ajacocks/mb386sx-rc2016/KiCad/AT386SX.kicad_sch

## KiCad design KiCad/AT386SX.kicad_sch (2026-02-18)

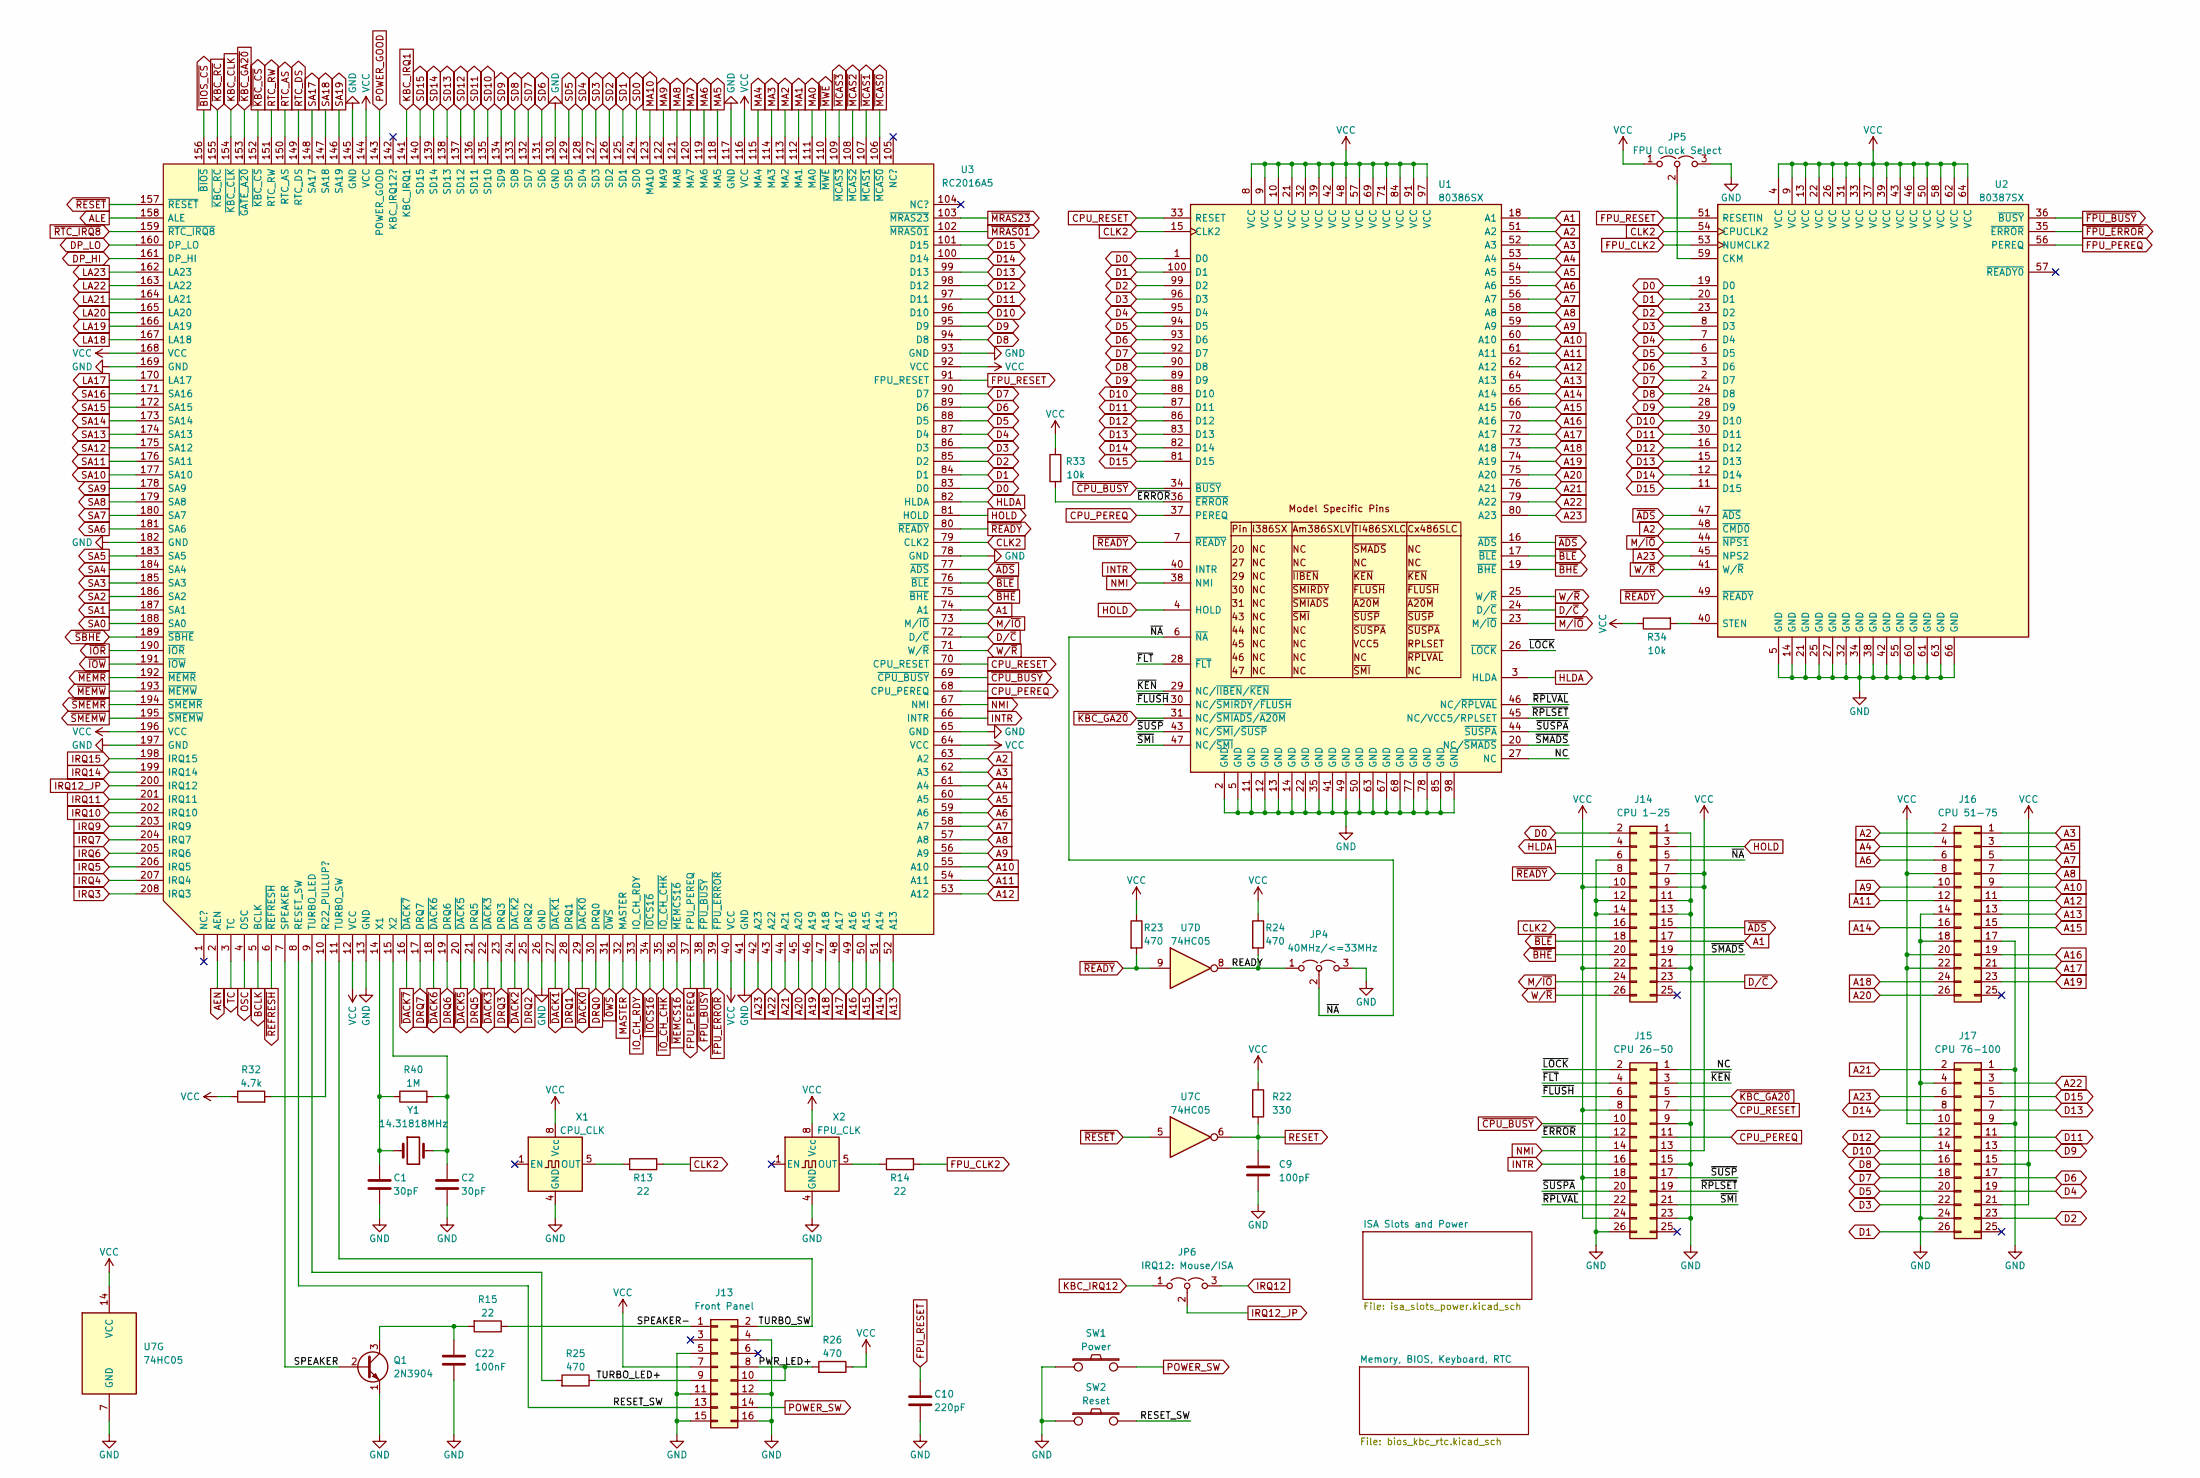
[picture p5: schematic AT386SX.kicad_sch]

Parts:
C1, C2: 30pF; Cap_Cer_508
C9: 100pF; Cap_Cer_508
C10: 220pF; Cap_Cer_508
C22: 100nF; Cap_Cer_508
J13: Front Panel; Conn_Pin_Header_8x2_2.54mm
J14: CPU 1-25; PinHeader_2x13_P2.00mm_Vertical
J15: CPU 26-50; PinHeader_2x13_P2.00mm_Vertical
J16: CPU 51-75; PinHeader_2x13_P2.00mm_Vertical
J17: CPU 76-100; PinHeader_2x13_P2.00mm_Vertical
JP4: 40MHz/<=33MHz; Conn_Pin_Header_3x1_2.54mm
JP5: FPU Clock Select; Conn_Pin_Header_3x1_2.54mm
JP6: IRQ12: Mouse/ISA; Conn_Pin_Header_3x1_2.54mm
Q1: 2N3904; Transistor_TO92_EBC_254
R13, R14, R15: 22; Res_762
R22: 330; Res_762
R23, R24, R25, R26: 470; Res_762
R32: 4.7k; Res_762
R33, R34: 10k; Res_762
R40: 1M; Res_762
SW1: Power; Switch_Tactile_6mm
SW2: Reset; Switch_Tactile_6mm
U1: 80386SX; PQFP-100_19x19mm_P0.635mm_i386sx
U2: 80387SX; IC_PLCC68_INTEL_TH
U3: RC2016A5; PQFP-208_28x28mm_P0.5mm
U7: 74HC05; IC_DIP14_300
X1: CPU_CLK; OSC_Half_Can_DIP8
X2: FPU_CLK; OSC_Half_Can_DIP8
Y1: 14.31818MHz; Crystal_HC-49U_Vert

Connections:
A1: J14.17, U1.18 (A1), U3.74 (A1)
A2: J16.2, U1.51 (A2), U2.48 (~CMD0), U3.63 (A2)
A3: J16.1, U1.52 (A3), U3.62 (A3)
A4: J16.4, U1.53 (A4), U3.61 (A4)
A5: J16.3, U1.54 (A5), U3.60 (A5)
A6: J16.6, U1.55 (A6), U3.59 (A6)
A7: J16.5, U1.56 (A7), U3.58 (A7)
A8: J16.7, U1.58 (A8), U3.57 (A8)
A9: J16.10, U1.59 (A9), U3.56 (A9)
A10: J16.9, U1.60 (A10), U3.55 (A10)
A11: J16.12, U1.61 (A11), U3.54 (A11)
A12: J16.11, U1.62 (A12), U3.53 (A12)
A13: J16.13, U1.64 (A13), U3.52 (A13)
A14: J16.16, U1.65 (A14), U3.51 (A14)
A15: J16.15, U1.66 (A15), U3.50 (A15)
A16: J16.19, U1.70 (A16), U3.49 (A16)
A17: J16.21, U1.72 (A17), U3.48 (A17)
A18: J16.24, U1.73 (A18), U3.47 (A18)
A19: J16.23, U1.74 (A19), U3.46 (A19)
A20: J16.26, U1.75 (A20), U3.45 (A20)
A21: J17.2, U1.76 (A21), U3.44 (A21)
A22: J17.3, U1.79 (A22), U3.43 (A22)
A23: J17.6, U1.80 (A23), U2.45 (NPS2), U3.42 (A23)
AEN: U3.2 (AEN)
ALE: U3.158 (ALE)
BCLK: U3.5 (BCLK)
CLK2: J14.16, R13.2, U1.15 (CLK2), U2.54 (CPUCLK2), U3.79 (CLK2)
CPU_PEREQ: J15.11, U1.37 (PEREQ), U3.68 (CPU_PEREQ)
CPU_RESET: J15.7, U1.33 (RESET), U3.70 (CPU_RESET)
D0: J14.2, U1.1 (D0), U2.19 (D0), U3.83 (D0)
D1: J17.26, U1.100 (D1), U2.20 (D1), U3.84 (D1)
D2: J17.23, U1.99 (D2), U2.23 (D2), U3.85 (D2)
D3: J17.22, U1.96 (D3), U2.8 (D3), U3.86 (D3)
D4: J17.19, U1.95 (D4), U2.7 (D4), U3.87 (D4)
D5: J17.20, U1.94 (D5), U2.6 (D5), U3.88 (D5)
D6: J17.17, U1.93 (D6), U2.3 (D6), U3.89 (D6)
D7: J17.18, U1.92 (D7), U2.2 (D7), U3.90 (D7)
D8: J17.16, U1.90 (D8), U2.24 (D8), U3.94 (D8)
D9: J17.13, U1.89 (D9), U2.28 (D9), U3.95 (D9)
D10: J17.14, U1.88 (D10), U2.29 (D10), U3.96 (D10)
D11: J17.11, U1.87 (D11), U2.30 (D11), U3.97 (D11)
D12: J17.12, U1.86 (D12), U2.16 (D12), U3.98 (D12)
D13: J17.7, U1.83 (D13), U2.15 (D13), U3.99 (D13)
D14: J17.8, U1.82 (D14), U2.12 (D14), U3.100 (D14)
D15: J17.5, U1.81 (D15), U2.11 (D15), U3.101 (D15)
DP_HI: U3.161 (DP_HI)
DP_LO: U3.160 (DP_LO)
DRQ0: U3.30 (DRQ0)
DRQ1: U3.28 (DRQ1)
DRQ2: U3.25 (DRQ2)
DRQ3: U3.23 (DRQ3)
DRQ5: U3.21 (DRQ5)
DRQ6: U3.19 (DRQ6)
DRQ7: U3.17 (DRQ7)
D/~C: J14.23, U1.24 (D/~C), U3.72 (D/~C)
FPU_CLK2: R14.2, U2.53 (NUMCLK2)
FPU_PEREQ: U2.56 (PEREQ), U3.37 (FPU_PEREQ)
FPU_RESET: C10.1, U2.51 (RESETIN), U3.91 (FPU_RESET)
GND: C1.2, C2.2, C9.2, C10.2, C22.2, J13.4, J13.5, J13.11, J13.12, J13.15, J13.16, J14.1, J14.6, J14.11, J14.12, J14.13, J14.14, J14.21, J15.9, J15.15, J15.23, J15.26, J16.14, J16.17, J16.18, J17.1, J17.4, J17.9, J17.24, JP4.3 (B), JP5.3 (B), Q1.1 (E), SW1.1, SW2.1, U1.2 (GND), U1.5 (GND), U1.11 (GND), U1.12 (GND), U1.13 (GND), U1.14 (GND), U1.22 (GND), U1.35 (GND), U1.41 (GND), U1.49 (GND), U1.50 (GND), U1.63 (GND), U1.67 (GND), U1.68 (GND), U1.77 (GND), U1.78 (GND), U1.85 (GND), U1.98 (GND), U2.5 (GND), U2.14 (GND), U2.21 (GND), U2.25 (GND), U2.27 (GND), U2.32 (GND), U2.34 (GND), U2.38 (GND), U2.42 (GND), U2.55 (GND), U2.60 (GND), U2.61 (GND), U2.63 (GND), U2.66 (GND), U3.13 (GND), U3.26 (GND), U3.41 (GND), U3.65 (GND), U3.78 (GND), U3.93 (GND), U3.117 (GND), U3.130 (GND), U3.145 (GND), U3.169 (GND), U3.182 (GND), U3.197 (GND), U7.7 (GND), X1.4 (GND), X2.4 (GND)
HLDA: J14.4, U1.3 (HLDA), U3.82 (HLDA)
HOLD: J14.3, U1.4 (HOLD), U3.81 (HOLD)
INTR: J15.16, U1.40 (INTR), U3.66 (INTR)
IO_CH_RDY: U3.33 (IO_CH_RDY)
IRQ3: U3.208 (IRQ3)
IRQ4: U3.207 (IRQ4)
IRQ5: U3.206 (IRQ5)
IRQ6: U3.205 (IRQ6)
IRQ7: U3.204 (IRQ7)
IRQ9: U3.203 (IRQ9)
IRQ10: U3.202 (IRQ10)
IRQ11: U3.201 (IRQ11)
IRQ12: JP6.3 (B)
IRQ12_JP: JP6.2 (C), U3.200 (IRQ12)
IRQ14: U3.199 (IRQ14)
IRQ15: U3.198 (IRQ15)
KBC_CLK: U3.154 (~KBC_CLK)
KBC_IRQ1: U3.141 (KBC_IRQ1)
KBC_IRQ12: JP6.1 (A)
LA17: U3.170 (LA17)
LA18: U3.167 (LA18)
LA19: U3.166 (LA19)
LA20: U3.165 (LA20)
LA21: U3.164 (LA21)
LA22: U3.163 (LA22)
LA23: U3.162 (LA23)
MA0: U3.111 (MA0)
MA1: U3.112 (MA1)
MA2: U3.113 (MA2)
MA3: U3.114 (MA3)
MA4: U3.115 (MA4)
MA5: U3.118 (MA5)
MA6: U3.119 (MA6)
MA7: U3.120 (MA7)
MA8: U3.121 (MA8)
MA9: U3.122 (MA9)
MA10: U3.123 (MA10)
MASTER: U3.32 (MASTER)
M/~IO: J14.24, U1.23 (M/~IO), U2.44 (~NPS1), U3.73 (M/~IO)
NC: J15.1, U1.27 (NC)
NMI: J15.14, U1.38 (NMI), U3.67 (NMI)
unnamed: C1.1, R40.1, U3.14 (X1), Y1.1
unnamed: C2.1, R40.2, U3.15 (X2), Y1.2
unnamed: C22.1, Q1.3 (C), R15.2
unnamed: JP5.2 (C), U2.59 (CKM)
unnamed: R13.1, X1.5 (OUT)
unnamed: R14.1, X2.5 (OUT)
unnamed: R25.2, U3.9 (TURBO_LED)
unnamed: R32.2, U3.10 (R22_PULLUP?)
unnamed: R34.2, U2.40 (STEN)
OSC: U3.4 (OSC)
POWER_GOOD: U3.143 (POWER_GOOD)
POWER_SW: J13.14, SW1.2
PWR_LED+: J13.8, J13.10, R26.2
READY: JP4.1 (A), R24.2, U7.8
RESET: C9.1, R22.2, U7.6
RESET_SW: J13.13, SW2.2, U3.8 (RESET_SW)
RTC_AS: U3.150 (RTC_AS)
RTC_DS: U3.149 (RTC_DS)
RTC_RW: U3.151 (RTC_RW)
SA0: U3.188 (SA0)
SA1: U3.187 (SA1)
SA2: U3.186 (SA2)
SA3: U3.185 (SA3)
SA4: U3.184 (SA4)
SA5: U3.183 (SA5)
SA6: U3.181 (SA6)
SA7: U3.180 (SA7)
SA8: U3.179 (SA8)
SA9: U3.178 (SA9)
SA10: U3.177 (SA10)
SA11: U3.176 (SA11)
SA12: U3.175 (SA12)
SA13: U3.174 (SA13)
SA14: U3.173 (SA14)
SA15: U3.172 (SA15)
SA16: U3.171 (SA16)
SA17: U3.148 (SA17)
SA18: U3.147 (SA18)
SA19: U3.146 (SA19)
SD0: U3.124 (SD0)
SD1: U3.125 (SD1)
SD2: U3.126 (SD2)
SD3: U3.127 (SD3)
SD4: U3.128 (SD4)
SD5: U3.129 (SD5)
SD6: U3.131 (SD6)
SD7: U3.132 (SD7)
SD8: U3.133 (SD8)
SD9: U3.134 (SD9)
SD10: U3.135 (SD10)
SD11: U3.136 (SD11)
SD12: U3.137 (SD12)
SD13: U3.138 (SD13)
SD14: U3.139 (SD14)
SD15: U3.140 (SD15)
SPEAKER: Q1.2 (B), U3.7 (SPEAKER)
SPEAKER-: J13.1, R15.1
TC: U3.3 (TC)
TURBO_LED+: J13.9, R25.1
TURBO_SW: J13.2, U3.11 (TURBO_SW)
VCC: J13.7, J14.7, J14.9, J14.10, J14.22, J15.8, J15.13, J15.18, J15.24, J16.8, J16.20, J16.22, J17.10, J17.15, J17.21, JP5.1 (A), R22.1, R23.1, R24.1, R26.1, R32.1, R33.1, R34.1, U1.8 (VCC), U1.9 (VCC), U1.10 (VCC), U1.21 (VCC), U1.32 (VCC), U1.39 (VCC), U1.42 (VCC), U1.48 (VCC), U1.57 (VCC), U1.69 (VCC), U1.71 (VCC), U1.84 (VCC), U1.91 (VCC), U1.97 (VCC), U2.4 (VCC), U2.9 (VCC), U2.13 (VCC), U2.22 (VCC), U2.26 (VCC), U2.31 (VCC), U2.33 (VCC), U2.37 (VCC), U2.39 (VCC), U2.43 (VCC), U2.46 (VCC), U2.50 (VCC), U2.58 (VCC), U2.62 (VCC), U2.64 (VCC), U3.12 (VCC), U3.40 (VCC), U3.64 (VCC), U3.92 (VCC), U3.116 (VCC), U3.144 (VCC), U3.168 (VCC), U3.196 (VCC), U7.14 (VCC), X1.8 (Vcc), X2.8 (Vcc)
W/~R: J14.26, U1.25 (W/~R), U2.41 (W/~R), U3.71 (W/~R)
~0WS: U3.31 (~0WS)
~ADS: J14.15, U1.16 (~ADS), U2.47 (~ADS), U3.77 (~ADS)
~BHE: J14.20, U1.19 (~BHE), U3.75 (~BHE)
~BIOS_CS: U3.156 (~BIOS)
~BLE: J14.18, U1.17 (~BLE), U3.76 (~BLE)
~CPU_BUSY: J15.10, U1.34 (~BUSY), U3.69 (~CPU_BUSY)
~DACK0: U3.29 (~DACK0)
~DACK1: U3.27 (~DACK1)
~DACK2: U3.24 (~DACK2)
~DACK3: U3.22 (~DACK3)
~DACK5: U3.20 (~DACK5)
~DACK6: U3.18 (~DACK6)
~DACK7: U3.16 (~DACK7)
~ERROR: J15.12, R33.2, U1.36 (~ERROR)
~FLT: J15.4, U1.28 (~FLT)
~FLUSH: J15.6, U1.30 (NC/~SMIRDY/~FLUSH)
~FPU_BUSY: U2.36 (~BUSY), U3.38 (~FPU_BUSY)
~FPU_ERROR: U2.35 (~ERROR), U3.39 (~FPU_ERROR)
~IOCS16: U3.34 (~IOCS16)
~IOR: U3.190 (~IOR)
~IOW: U3.191 (~IOW)
~IO_CH_CHK: U3.35 (~IO_CH_CHK)
~KBC_CS: U3.152 (~KBC_CS)
~KBC_GA20: J15.5, U1.31 (NC/~SMIADS/~A20M), U3.153 (~GATE_A20)
~KBC_RC: U3.155 (~KBC_RC)
~KEN: J15.3, U1.29 (NC/~IIBEN/~KEN)
~LOCK: J15.2, U1.26 (~LOCK)
~MCAS0: U3.106 (~MCAS0)
~MCAS1: U3.107 (~MCAS1)
~MCAS2: U3.108 (~MCAS2)
~MCAS3: U3.109 (~MCAS3)
~MEMCS16: U3.36 (~MEMCS16)
~MEMR: U3.192 (~MEMR)
~MEMW: U3.193 (~MEMW)
~MRAS01: U3.102 (~MRAS01)
~MRAS23: U3.103 (~MRAS23)
~MWE: U3.110 (~MWE)
~NA: J14.5, JP4.2 (C), U1.6 (~NA)
~READY: J14.8, R23.2, U1.7 (~READY), U2.49 (~READY), U3.80 (~READY), U7.9
~REFRESH: U3.6 (~REFRESH)
~RESET: U3.157 (~RESET), U7.5
~RPLSET: J15.19, U1.45 (NC/VCC5/RPLSET)
~RPLVAL: J15.22, U1.46 (NC/~RPLVAL)
~RTC_IRQ8: U3.159 (~RTC_IRQ8)
~SBHE: U3.189 (~SBHE)
~SMADS: J14.19, U1.20 (NC/~SMADS)
~SMEMR: U3.194 (~SMEMR)
~SMEMW: U3.195 (~SMEMW)
~SMI: J15.21, U1.47 (NC/~SMI)
~SUSPA: J15.20, U1.44 (~SUSPA)
~SUSP: J15.17, U1.43 (NC/~SMI/~SUSP)
