ajacocks/mb386sx-rc2016/KiCad/bios_kbc_rtc.kicad_sch

## KiCad design KiCad/bios_kbc_rtc.kicad_sch (2026-02-17)

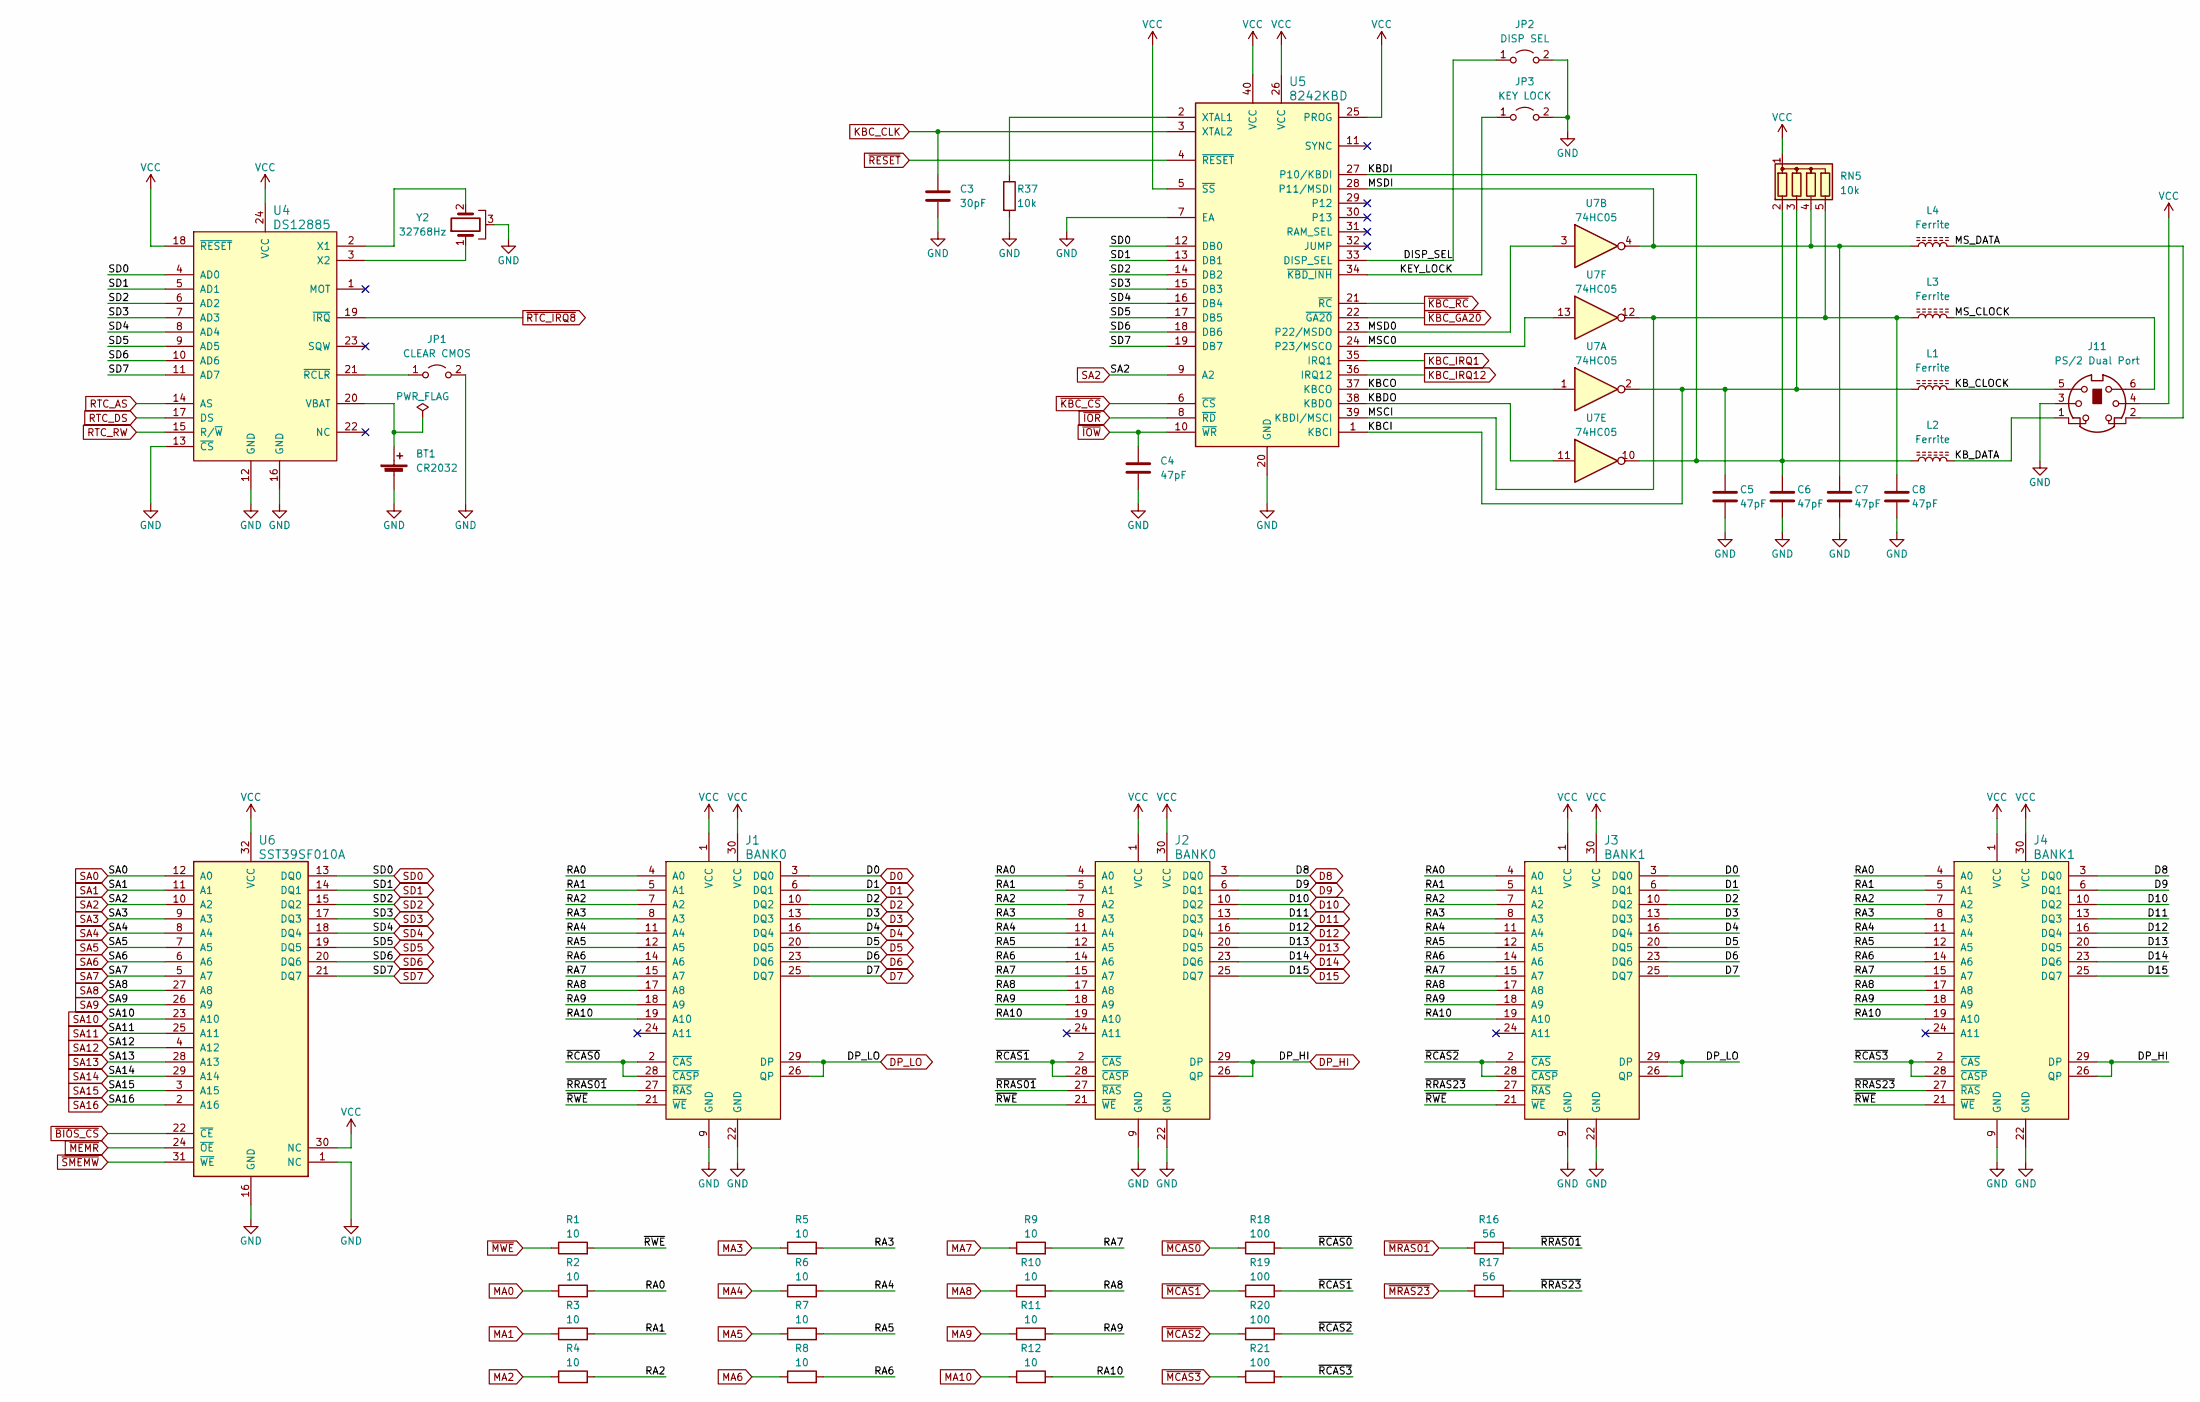
[picture p6: schematic bios_kbc_rtc.kicad_sch]

Parts:
BT1: CR2032; Battery_Holder_CR2032_Universal
C3: 30pF; Cap_Cer_508
C4, C5, C6, C7, C8: 47pF; Cap_Cer_508
J1, J2: BANK0; Conn_SIMM30
J3, J4: BANK1; Conn_SIMM30
J11: PS/2 Dual Port; Conn_Mini_DIN_6pin
JP1: CLEAR CMOS; Conn_Pin_Header_2x1_2.54mm
JP2: DISP SEL; Conn_Pin_Header_2x1_2.54mm
JP3: KEY LOCK; Conn_Pin_Header_2x1_2.54mm
L1, L2, L3, L4: Ferrite; L_Ferrite_1016
R1, R2, R3, R4, R5, R6, R7, R8, R9, R10, R11, R12: 10; Res_762
R16, R17: 56; Res_762
R18, R19, R20, R21: 100; Res_762
R37: 10k; Res_762
RN5: 10k; Conn_SIL5
U4: DS12885; IC_DIP24_600
U5: 8242KBD; IC_DIP40_600
U6: SST39SF010A; IC_DIP32_600
U7: 74HC05; IC_DIP14_300
Y2: 32768Hz; Crystal_32K_Horiz

Connections:
D0: J1.3 (DQ0), J3.3 (DQ0)
D1: J1.6 (DQ1), J3.6 (DQ1)
D2: J1.10 (DQ2), J3.10 (DQ2)
D3: J1.13 (DQ3), J3.13 (DQ3)
D4: J1.16 (DQ4), J3.16 (DQ4)
D5: J1.20 (DQ5), J3.20 (DQ5)
D6: J1.23 (DQ6), J3.23 (DQ6)
D7: J1.25 (DQ7), J3.25 (DQ7)
D8: J2.3 (DQ0), J4.3 (DQ0)
D9: J2.6 (DQ1), J4.6 (DQ1)
D10: J2.10 (DQ2), J4.10 (DQ2)
D11: J2.13 (DQ3), J4.13 (DQ3)
D12: J2.16 (DQ4), J4.16 (DQ4)
D13: J2.20 (DQ5), J4.20 (DQ5)
D14: J2.23 (DQ6), J4.23 (DQ6)
D15: J2.25 (DQ7), J4.25 (DQ7)
DISP_SEL: JP2.1 (A), U5.33 (DISP_SEL)
DP_HI: J2.26 (QP), J2.29 (DP), J4.26 (QP), J4.29 (DP)
DP_LO: J1.26 (QP), J1.29 (DP), J3.26 (QP), J3.29 (DP)
GND: BT1.2 (-), C3.2, C4.2, C5.2, C6.2, C7.2, C8.2, J1.9 (GND), J1.22 (GND), J2.9 (GND), J2.22 (GND), J3.9 (GND), J3.22 (GND), J4.9 (GND), J4.22 (GND), J11.3, JP1.2 (B), JP2.2 (B), JP3.2 (B), R37.2, U4.12 (GND), U4.13 (~CS), U4.16 (GND), U5.7 (EA), U5.20 (GND), U6.1 (NC), U6.16 (GND), Y2.3
KBCI: C5.1, L1.1, RN5.3 (R2), U5.1 (KBCI), U7.2
KBCO: U5.37 (KBCO), U7.1
KBC_CLK: C3.1, U5.3 (XTAL2)
KBC_IRQ1: U5.35 (IRQ1)
KBC_IRQ12: U5.36 (IRQ12)
KBDI: C6.1, L2.1, RN5.2 (R1), U5.27 (P10/KBDI), U7.10
KBDO: U5.38 (KBDO), U7.11
KB_CLOCK: J11.5, L1.2
KB_DATA: J11.1, L2.2
KEY_LOCK: JP3.1 (A), U5.34 (~KBD_INH)
MA0: R2.1
MA1: R3.1
MA2: R4.1
MA3: R5.1
MA4: R6.1
MA5: R7.1
MA6: R8.1
MA7: R9.1
MA8: R10.1
MA9: R11.1
MA10: R12.1
MSC0: U5.24 (P23/MSCO), U7.13
MSCI: C8.1, L3.1, RN5.5 (R4), U5.39 (KBDI/MSCI), U7.12
MSD0: U5.23 (P22/MSDO), U7.3
MSDI: C7.1, L4.1, RN5.4 (R3), U5.28 (P11/MSDI), U7.4
MS_CLOCK: J11.6, L3.2
MS_DATA: J11.2, L4.2
unnamed: BT1.1 (+), U4.20 (VBAT)
unnamed: JP1.1 (A), U4.21 (~RCLR)
unnamed: R37.1, U5.2 (XTAL1)
unnamed: U4.2 (X1), Y2.2
unnamed: U4.3 (X2), Y2.1
RA0: J1.4 (A0), J2.4 (A0), J3.4 (A0), J4.4 (A0), R2.2
RA1: J1.5 (A1), J2.5 (A1), J3.5 (A1), J4.5 (A1), R3.2
RA2: J1.7 (A2), J2.7 (A2), J3.7 (A2), J4.7 (A2), R4.2
RA3: J1.8 (A3), J2.8 (A3), J3.8 (A3), J4.8 (A3), R5.2
RA4: J1.11 (A4), J2.11 (A4), J3.11 (A4), J4.11 (A4), R6.2
RA5: J1.12 (A5), J2.12 (A5), J3.12 (A5), J4.12 (A5), R7.2
RA6: J1.14 (A6), J2.14 (A6), J3.14 (A6), J4.14 (A6), R8.2
RA7: J1.15 (A7), J2.15 (A7), J3.15 (A7), J4.15 (A7), R9.2
RA8: J1.17 (A8), J2.17 (A8), J3.17 (A8), J4.17 (A8), R10.2
RA9: J1.18 (A9), J2.18 (A9), J3.18 (A9), J4.18 (A9), R11.2
RA10: J1.19 (A10), J2.19 (A10), J3.19 (A10), J4.19 (A10), R12.2
RTC_AS: U4.14 (AS)
RTC_DS: U4.17 (DS)
RTC_RW: U4.15 (R/~W)
SA0: U6.12 (A0)
SA1: U6.11 (A1)
SA2: U5.9 (A2), U6.10 (A2)
SA3: U6.9 (A3)
SA4: U6.8 (A4)
SA5: U6.7 (A5)
SA6: U6.6 (A6)
SA7: U6.5 (A7)
SA8: U6.27 (A8)
SA9: U6.26 (A9)
SA10: U6.23 (A10)
SA11: U6.25 (A11)
SA12: U6.4 (A12)
SA13: U6.28 (A13)
SA14: U6.29 (A14)
SA15: U6.3 (A15)
SA16: U6.2 (A16)
SD0: U4.4 (AD0), U5.12 (DB0), U6.13 (DQ0)
SD1: U4.5 (AD1), U5.13 (DB1), U6.14 (DQ1)
SD2: U4.6 (AD2), U5.14 (DB2), U6.15 (DQ2)
SD3: U4.7 (AD3), U5.15 (DB3), U6.17 (DQ3)
SD4: U4.8 (AD4), U5.16 (DB4), U6.18 (DQ4)
SD5: U4.9 (AD5), U5.17 (DB5), U6.19 (DQ5)
SD6: U4.10 (AD6), U5.18 (DB6), U6.20 (DQ6)
SD7: U4.11 (AD7), U5.19 (DB7), U6.21 (DQ7)
VCC: J1.1 (VCC), J1.30 (VCC), J2.1 (VCC), J2.30 (VCC), J3.1 (VCC), J3.30 (VCC), J4.1 (VCC), J4.30 (VCC), J11.4, RN5.1 (common), U4.18 (~RESET), U4.24 (VCC), U5.5 (~SS), U5.25 (PROG), U5.26 (VCC), U5.40 (VCC), U6.30 (NC), U6.32 (VCC)
~BIOS_CS: U6.22 (~CE)
~IOR: U5.8 (~RD)
~IOW: C4.1, U5.10 (~WR)
~KBC_CS: U5.6 (~CS)
~KBC_GA20: U5.22 (~GA20)
~KBC_RC: U5.21 (~RC)
~MCAS0: R18.1
~MCAS1: R19.1
~MCAS2: R20.1
~MCAS3: R21.1
~MEMR: U6.24 (~OE)
~MRAS01: R16.1
~MRAS23: R17.1
~MWE: R1.1
~RCAS0: J1.2 (~CAS), J1.28 (~CASP), R18.2
~RCAS1: J2.2 (~CAS), J2.28 (~CASP), R19.2
~RCAS2: J3.2 (~CAS), J3.28 (~CASP), R20.2
~RCAS3: J4.2 (~CAS), J4.28 (~CASP), R21.2
~RESET: U5.4 (~RESET)
~RRAS01: J1.27 (~RAS), J2.27 (~RAS), R16.2
~RRAS23: J3.27 (~RAS), J4.27 (~RAS), R17.2
~RTC_IRQ8: U4.19 (~IRQ)
~RWE: J1.21 (~WE), J2.21 (~WE), J3.21 (~WE), J4.21 (~WE), R1.2
~SMEMW: U6.31 (~WE)
