ajacocks/mb386sx-rc2016/KiCad/isa_slots_power.kicad_sch

## KiCad design KiCad/isa_slots_power.kicad_sch (2026-02-18)

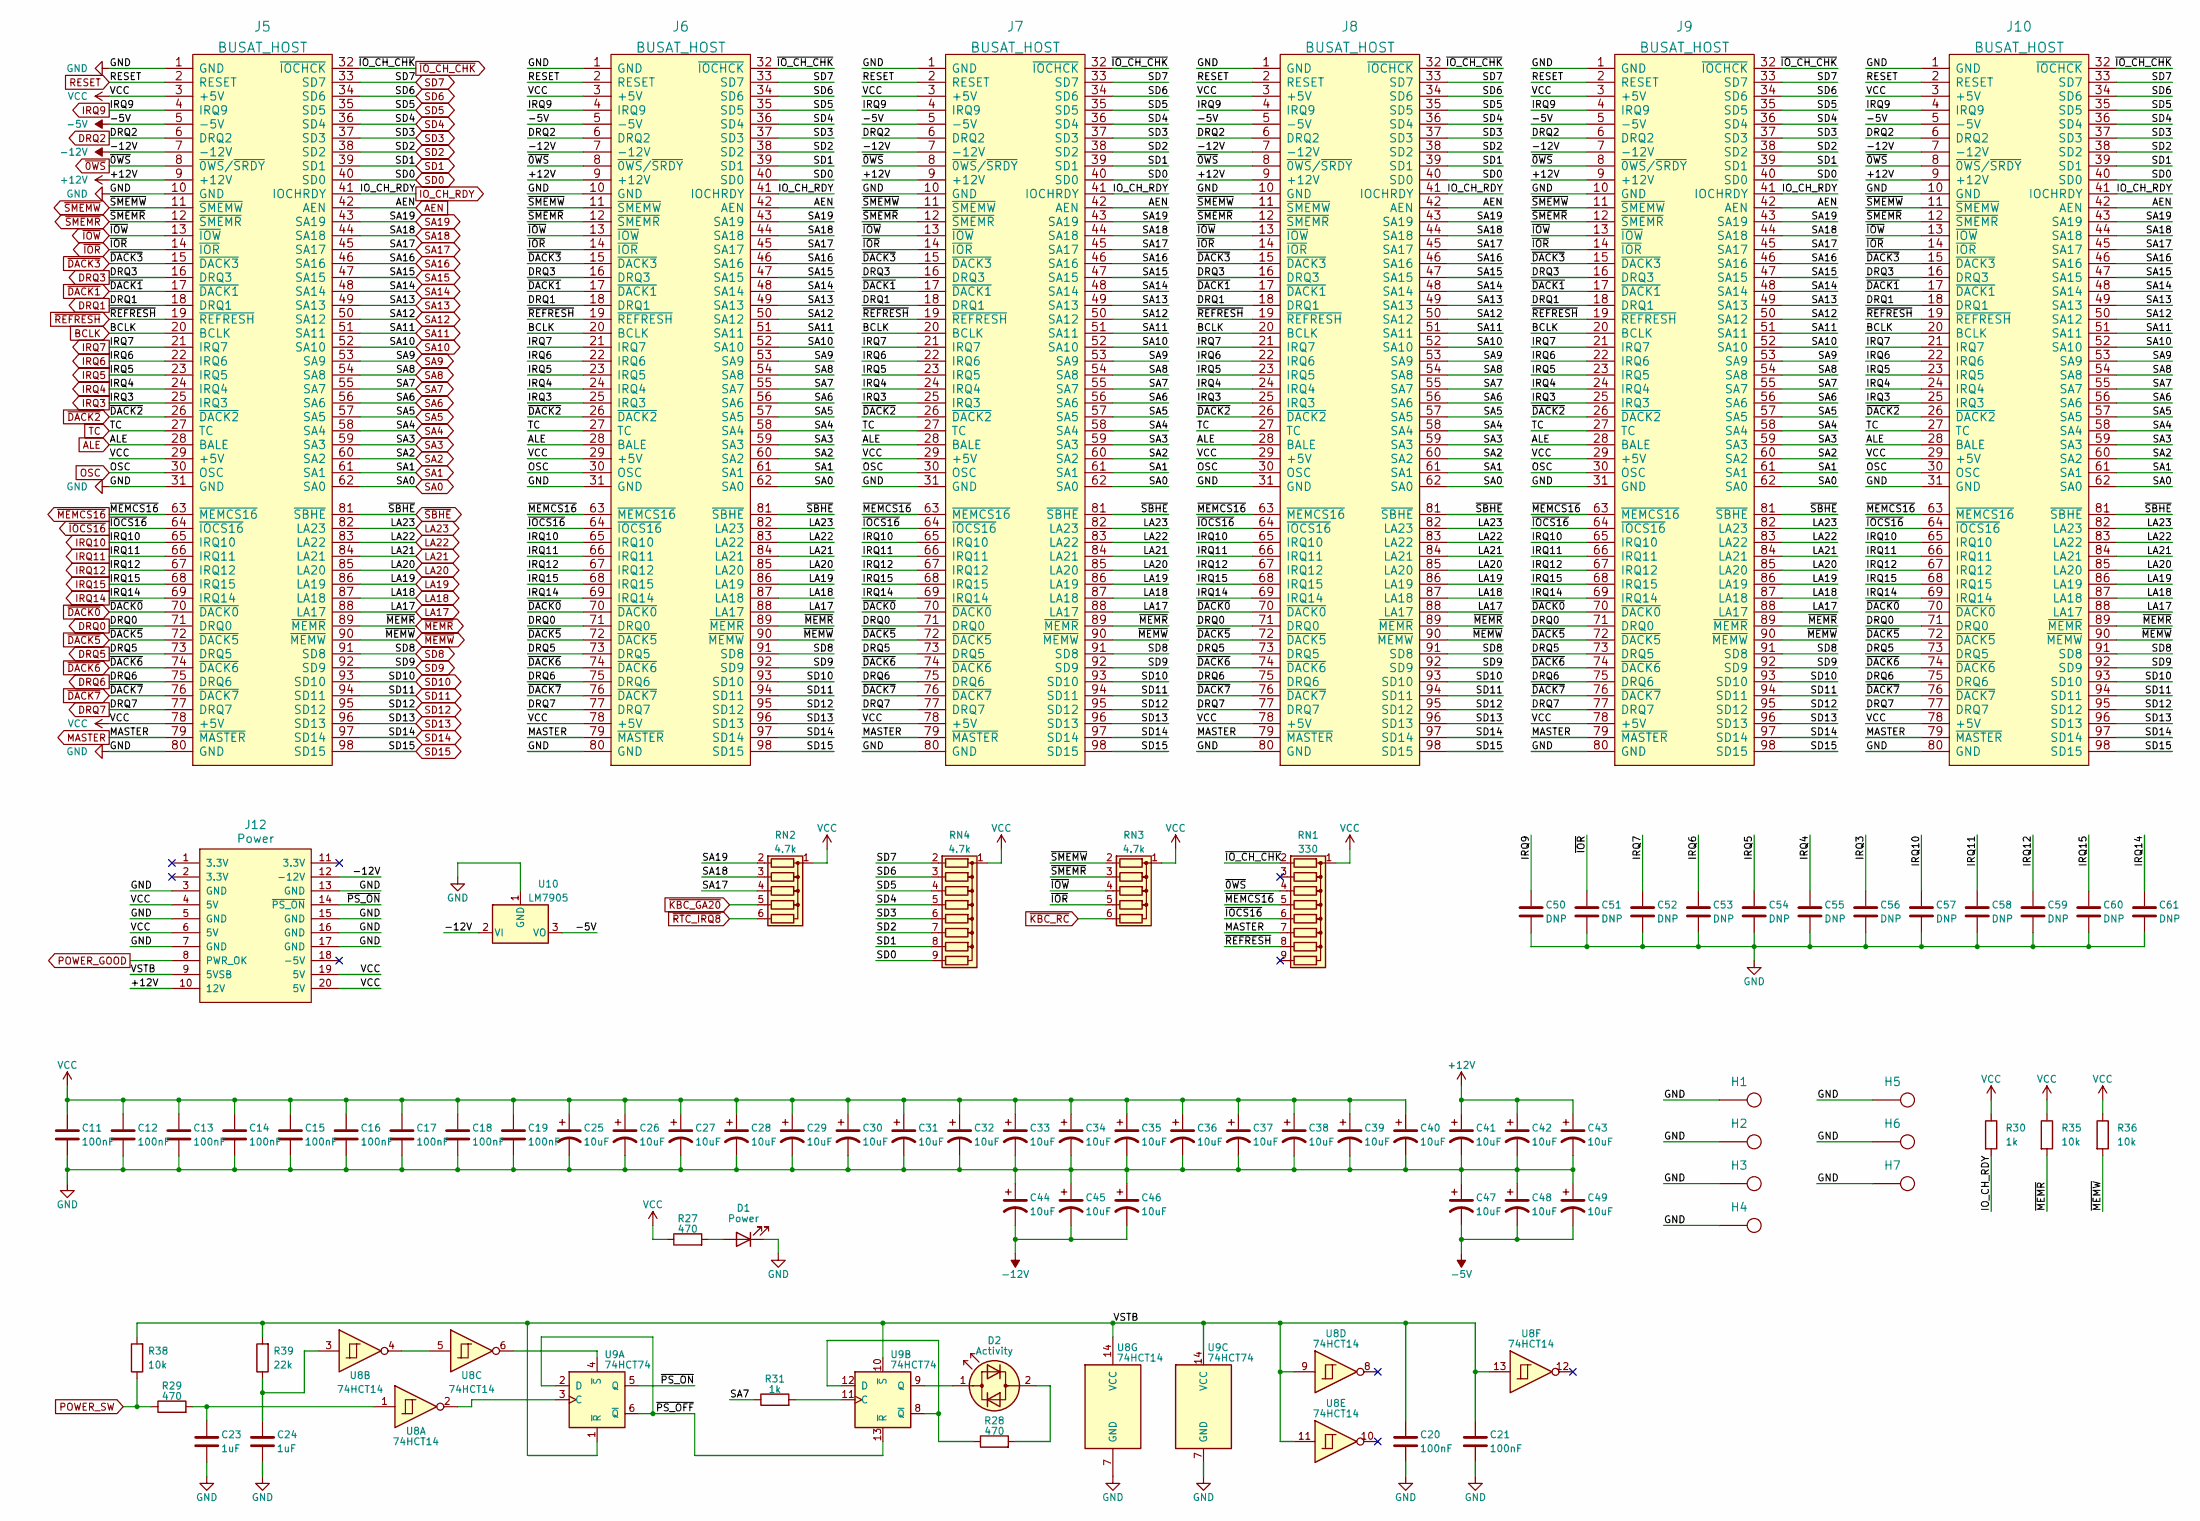
[picture p7: schematic isa_slots_power.kicad_sch]

Parts:
C11, C12, C13, C14, C15, C16, C17, C18, C19, C20, C21: 100nF; Cap_Cer_508
C23, C24: 1uF; Cap_Cer_508
C25, C26, C27, C28, C29, C30, C31, C32, C33, C34, C35, C36, C37, C38, C39, C40, C41, C42, C43, C44, C45, C46, C47, C48, C49: 10uF; Cap_Elec_Radial_5mm_2.5mm
C50, C51, C52, C53, C54, C55, C56, C57, C58, C59, C60, C61: DNP; Cap_Cer_508
D1: Power; LED_3mm
D2: Activity; LED_3mm
H1, H2, H3, H4, H5, H6, H7: HOLE; MountingHole_4mm_Pad_Via
J5, J6, J7, J8, J9, J10: BUSAT_HOST; Conn_Edge_ISA16
J12: Power; Conn_Power_ATX_20pin
R27, R28, R29: 470; Res_762
R30, R31: 1k; Res_762
R35, R36, R38: 10k; Res_762
R39: 22k; Res_762
RN1: 330; Conn_SIL9
RN2, RN3: 4.7k; Conn_SIL6
RN4: 4.7k; Conn_SIL9
U8: 74HCT14; IC_DIP14_300
U9: 74HCT74; IC_DIP14_300
U10: LM7905; IC_TO220-3_Vert

Connections:
+12V: C41.1, C42.1, C43.1, J5.9 (+12V), J6.9 (+12V), J7.9 (+12V), J8.9 (+12V), J9.9 (+12V), J10.9 (+12V), J12.10 (12V)
-5V: C47.2, C48.2, C49.2, J5.5 (-5V), J6.5 (-5V), J7.5 (-5V), J8.5 (-5V), J9.5 (-5V), J10.5 (-5V), U10.3 (VO)
-12V: C44.2, C45.2, C46.2, J5.7 (-12V), J6.7 (-12V), J7.7 (-12V), J8.7 (-12V), J9.7 (-12V), J10.7 (-12V), J12.12 (-12V), U10.2 (VI)
AEN: J5.42 (AEN), J6.42 (AEN), J7.42 (AEN), J8.42 (AEN), J9.42 (AEN), J10.42 (AEN)
ALE: J5.28 (BALE), J6.28 (BALE), J7.28 (BALE), J8.28 (BALE), J9.28 (BALE), J10.28 (BALE)
BCLK: J5.20 (BCLK), J6.20 (BCLK), J7.20 (BCLK), J8.20 (BCLK), J9.20 (BCLK), J10.20 (BCLK)
DRQ0: J5.71 (DRQ0), J6.71 (DRQ0), J7.71 (DRQ0), J8.71 (DRQ0), J9.71 (DRQ0), J10.71 (DRQ0)
DRQ1: J5.18 (DRQ1), J6.18 (DRQ1), J7.18 (DRQ1), J8.18 (DRQ1), J9.18 (DRQ1), J10.18 (DRQ1)
DRQ2: J5.6 (DRQ2), J6.6 (DRQ2), J7.6 (DRQ2), J8.6 (DRQ2), J9.6 (DRQ2), J10.6 (DRQ2)
DRQ3: J5.16 (DRQ3), J6.16 (DRQ3), J7.16 (DRQ3), J8.16 (DRQ3), J9.16 (DRQ3), J10.16 (DRQ3)
DRQ5: J5.73 (DRQ5), J6.73 (DRQ5), J7.73 (DRQ5), J8.73 (DRQ5), J9.73 (DRQ5), J10.73 (DRQ5)
DRQ6: J5.75 (DRQ6), J6.75 (DRQ6), J7.75 (DRQ6), J8.75 (DRQ6), J9.75 (DRQ6), J10.75 (DRQ6)
DRQ7: J5.77 (DRQ7), J6.77 (DRQ7), J7.77 (DRQ7), J8.77 (DRQ7), J9.77 (DRQ7), J10.77 (DRQ7)
GND: C11.2, C12.2, C13.2, C14.2, C15.2, C16.2, C17.2, C18.2, C19.2, C20.2, C21.2, C23.2, C24.2, C25.2, C26.2, C27.2, C28.2, C29.2, C30.2, C31.2, C32.2, C33.2, C34.2, C35.2, C36.2, C37.2, C38.2, C39.2, C40.2, C41.2, C42.2, C43.2, C44.1, C45.1, C46.1, C47.1, C48.1, C49.1, C50.2, C51.2, C52.2, C53.2, C54.2, C55.2, C56.2, C57.2, C58.2, C59.2, C60.2, C61.2, D1.1 (K), H1.1, H2.1, H3.1, H4.1, H5.1, H6.1, H7.1, J5.1 (GND), J5.10 (GND), J5.31 (GND), J5.80 (GND), J6.1 (GND), J6.10 (GND), J6.31 (GND), J6.80 (GND), J7.1 (GND), J7.10 (GND), J7.31 (GND), J7.80 (GND), J8.1 (GND), J8.10 (GND), J8.31 (GND), J8.80 (GND), J9.1 (GND), J9.10 (GND), J9.31 (GND), J9.80 (GND), J10.1 (GND), J10.10 (GND), J10.31 (GND), J10.80 (GND), J12.3 (GND), J12.5 (GND), J12.7 (GND), J12.13 (GND), J12.15 (GND), J12.16 (GND), J12.17 (GND), U8.7 (GND), U9.7 (GND), U10.1 (GND)
IO_CH_RDY: J5.41 (IOCHRDY), J6.41 (IOCHRDY), J7.41 (IOCHRDY), J8.41 (IOCHRDY), J9.41 (IOCHRDY), J10.41 (IOCHRDY), R30.2
IRQ3: C56.1, J5.25 (IRQ3), J6.25 (IRQ3), J7.25 (IRQ3), J8.25 (IRQ3), J9.25 (IRQ3), J10.25 (IRQ3)
IRQ4: C55.1, J5.24 (IRQ4), J6.24 (IRQ4), J7.24 (IRQ4), J8.24 (IRQ4), J9.24 (IRQ4), J10.24 (IRQ4)
IRQ5: C54.1, J5.23 (IRQ5), J6.23 (IRQ5), J7.23 (IRQ5), J8.23 (IRQ5), J9.23 (IRQ5), J10.23 (IRQ5)
IRQ6: C53.1, J5.22 (IRQ6), J6.22 (IRQ6), J7.22 (IRQ6), J8.22 (IRQ6), J9.22 (IRQ6), J10.22 (IRQ6)
IRQ7: C52.1, J5.21 (IRQ7), J6.21 (IRQ7), J7.21 (IRQ7), J8.21 (IRQ7), J9.21 (IRQ7), J10.21 (IRQ7)
IRQ9: C50.1, J5.4 (IRQ9), J6.4 (IRQ9), J7.4 (IRQ9), J8.4 (IRQ9), J9.4 (IRQ9), J10.4 (IRQ9)
IRQ10: C57.1, J5.65 (IRQ10), J6.65 (IRQ10), J7.65 (IRQ10), J8.65 (IRQ10), J9.65 (IRQ10), J10.65 (IRQ10)
IRQ11: C58.1, J5.66 (IRQ11), J6.66 (IRQ11), J7.66 (IRQ11), J8.66 (IRQ11), J9.66 (IRQ11), J10.66 (IRQ11)
IRQ12: C59.1, J5.67 (IRQ12), J6.67 (IRQ12), J7.67 (IRQ12), J8.67 (IRQ12), J9.67 (IRQ12), J10.67 (IRQ12)
IRQ14: C61.1, J5.69 (IRQ14), J6.69 (IRQ14), J7.69 (IRQ14), J8.69 (IRQ14), J9.69 (IRQ14), J10.69 (IRQ14)
IRQ15: C60.1, J5.68 (IRQ15), J6.68 (IRQ15), J7.68 (IRQ15), J8.68 (IRQ15), J9.68 (IRQ15), J10.68 (IRQ15)
LA17: J5.88 (LA17), J6.88 (LA17), J7.88 (LA17), J8.88 (LA17), J9.88 (LA17), J10.88 (LA17)
LA18: J5.87 (LA18), J6.87 (LA18), J7.87 (LA18), J8.87 (LA18), J9.87 (LA18), J10.87 (LA18)
LA19: J5.86 (LA19), J6.86 (LA19), J7.86 (LA19), J8.86 (LA19), J9.86 (LA19), J10.86 (LA19)
LA20: J5.85 (LA20), J6.85 (LA20), J7.85 (LA20), J8.85 (LA20), J9.85 (LA20), J10.85 (LA20)
LA21: J5.84 (LA21), J6.84 (LA21), J7.84 (LA21), J8.84 (LA21), J9.84 (LA21), J10.84 (LA21)
LA22: J5.83 (LA22), J6.83 (LA22), J7.83 (LA22), J8.83 (LA22), J9.83 (LA22), J10.83 (LA22)
LA23: J5.82 (LA23), J6.82 (LA23), J7.82 (LA23), J8.82 (LA23), J9.82 (LA23), J10.82 (LA23)
MASTER: J5.79 (~MASTER), J6.79 (~MASTER), J7.79 (~MASTER), J8.79 (~MASTER), J9.79 (~MASTER), J10.79 (~MASTER), RN1.7 (R6)
unnamed: C23.1, R29.2, U8.1
unnamed: C24.1, R39.1, U8.3
unnamed: D1.2 (A), R27.2
unnamed: D2.1 (KA), U9.9 (Q)
unnamed: D2.2 (AK), R28.2
unnamed: R28.1, U9.8 (~Q), U9.12 (D)
unnamed: R31.2, U9.11 (C)
unnamed: U8.2, U9.3 (C)
unnamed: U8.4, U8.5
unnamed: U8.6, U9.4 (~S)
OSC: J5.30 (OSC), J6.30 (OSC), J7.30 (OSC), J8.30 (OSC), J9.30 (OSC), J10.30 (OSC)
POWER_GOOD: J12.8 (PWR_OK)
POWER_SW: R29.1, R38.1
RESET: J5.2 (RESET), J6.2 (RESET), J7.2 (RESET), J8.2 (RESET), J9.2 (RESET), J10.2 (RESET)
SA0: J5.62 (SA0), J6.62 (SA0), J7.62 (SA0), J8.62 (SA0), J9.62 (SA0), J10.62 (SA0)
SA1: J5.61 (SA1), J6.61 (SA1), J7.61 (SA1), J8.61 (SA1), J9.61 (SA1), J10.61 (SA1)
SA2: J5.60 (SA2), J6.60 (SA2), J7.60 (SA2), J8.60 (SA2), J9.60 (SA2), J10.60 (SA2)
SA3: J5.59 (SA3), J6.59 (SA3), J7.59 (SA3), J8.59 (SA3), J9.59 (SA3), J10.59 (SA3)
SA4: J5.58 (SA4), J6.58 (SA4), J7.58 (SA4), J8.58 (SA4), J9.58 (SA4), J10.58 (SA4)
SA5: J5.57 (SA5), J6.57 (SA5), J7.57 (SA5), J8.57 (SA5), J9.57 (SA5), J10.57 (SA5)
SA6: J5.56 (SA6), J6.56 (SA6), J7.56 (SA6), J8.56 (SA6), J9.56 (SA6), J10.56 (SA6)
SA7: J5.55 (SA7), J6.55 (SA7), J7.55 (SA7), J8.55 (SA7), J9.55 (SA7), J10.55 (SA7), R31.1
SA8: J5.54 (SA8), J6.54 (SA8), J7.54 (SA8), J8.54 (SA8), J9.54 (SA8), J10.54 (SA8)
SA9: J5.53 (SA9), J6.53 (SA9), J7.53 (SA9), J8.53 (SA9), J9.53 (SA9), J10.53 (SA9)
SA10: J5.52 (SA10), J6.52 (SA10), J7.52 (SA10), J8.52 (SA10), J9.52 (SA10), J10.52 (SA10)
SA11: J5.51 (SA11), J6.51 (SA11), J7.51 (SA11), J8.51 (SA11), J9.51 (SA11), J10.51 (SA11)
SA12: J5.50 (SA12), J6.50 (SA12), J7.50 (SA12), J8.50 (SA12), J9.50 (SA12), J10.50 (SA12)
SA13: J5.49 (SA13), J6.49 (SA13), J7.49 (SA13), J8.49 (SA13), J9.49 (SA13), J10.49 (SA13)
SA14: J5.48 (SA14), J6.48 (SA14), J7.48 (SA14), J8.48 (SA14), J9.48 (SA14), J10.48 (SA14)
SA15: J5.47 (SA15), J6.47 (SA15), J7.47 (SA15), J8.47 (SA15), J9.47 (SA15), J10.47 (SA15)
SA16: J5.46 (SA16), J6.46 (SA16), J7.46 (SA16), J8.46 (SA16), J9.46 (SA16), J10.46 (SA16)
SA17: J5.45 (SA17), J6.45 (SA17), J7.45 (SA17), J8.45 (SA17), J9.45 (SA17), J10.45 (SA17), RN2.4 (R3)
SA18: J5.44 (SA18), J6.44 (SA18), J7.44 (SA18), J8.44 (SA18), J9.44 (SA18), J10.44 (SA18), RN2.3 (R2)
SA19: J5.43 (SA19), J6.43 (SA19), J7.43 (SA19), J8.43 (SA19), J9.43 (SA19), J10.43 (SA19), RN2.2 (R1)
SD0: J5.40 (SD0), J6.40 (SD0), J7.40 (SD0), J8.40 (SD0), J9.40 (SD0), J10.40 (SD0), RN4.9 (R8)
SD1: J5.39 (SD1), J6.39 (SD1), J7.39 (SD1), J8.39 (SD1), J9.39 (SD1), J10.39 (SD1), RN4.8 (R7)
SD2: J5.38 (SD2), J6.38 (SD2), J7.38 (SD2), J8.38 (SD2), J9.38 (SD2), J10.38 (SD2), RN4.7 (R6)
SD3: J5.37 (SD3), J6.37 (SD3), J7.37 (SD3), J8.37 (SD3), J9.37 (SD3), J10.37 (SD3), RN4.6 (R5)
SD4: J5.36 (SD4), J6.36 (SD4), J7.36 (SD4), J8.36 (SD4), J9.36 (SD4), J10.36 (SD4), RN4.5 (R4)
SD5: J5.35 (SD5), J6.35 (SD5), J7.35 (SD5), J8.35 (SD5), J9.35 (SD5), J10.35 (SD5), RN4.4 (R3)
SD6: J5.34 (SD6), J6.34 (SD6), J7.34 (SD6), J8.34 (SD6), J9.34 (SD6), J10.34 (SD6), RN4.3 (R2)
SD7: J5.33 (SD7), J6.33 (SD7), J7.33 (SD7), J8.33 (SD7), J9.33 (SD7), J10.33 (SD7), RN4.2 (R1)
SD8: J5.91 (SD8), J6.91 (SD8), J7.91 (SD8), J8.91 (SD8), J9.91 (SD8), J10.91 (SD8)
SD9: J5.92 (SD9), J6.92 (SD9), J7.92 (SD9), J8.92 (SD9), J9.92 (SD9), J10.92 (SD9)
SD10: J5.93 (SD10), J6.93 (SD10), J7.93 (SD10), J8.93 (SD10), J9.93 (SD10), J10.93 (SD10)
SD11: J5.94 (SD11), J6.94 (SD11), J7.94 (SD11), J8.94 (SD11), J9.94 (SD11), J10.94 (SD11)
SD12: J5.95 (SD12), J6.95 (SD12), J7.95 (SD12), J8.95 (SD12), J9.95 (SD12), J10.95 (SD12)
SD13: J5.96 (SD13), J6.96 (SD13), J7.96 (SD13), J8.96 (SD13), J9.96 (SD13), J10.96 (SD13)
SD14: J5.97 (SD14), J6.97 (SD14), J7.97 (SD14), J8.97 (SD14), J9.97 (SD14), J10.97 (SD14)
SD15: J5.98 (SD15), J6.98 (SD15), J7.98 (SD15), J8.98 (SD15), J9.98 (SD15), J10.98 (SD15)
TC: J5.27 (TC), J6.27 (TC), J7.27 (TC), J8.27 (TC), J9.27 (TC), J10.27 (TC)
VCC: C11.1, C12.1, C13.1, C14.1, C15.1, C16.1, C17.1, C18.1, C19.1, C25.1, C26.1, C27.1, C28.1, C29.1, C30.1, C31.1, C32.1, C33.1, C34.1, C35.1, C36.1, C37.1, C38.1, C39.1, C40.1, J5.3 (+5V), J5.29 (+5V), J5.78 (+5V), J6.3 (+5V), J6.29 (+5V), J6.78 (+5V), J7.3 (+5V), J7.29 (+5V), J7.78 (+5V), J8.3 (+5V), J8.29 (+5V), J8.78 (+5V), J9.3 (+5V), J9.29 (+5V), J9.78 (+5V), J10.3 (+5V), J10.29 (+5V), J10.78 (+5V), J12.4 (5V), J12.6 (5V), J12.19 (5V), J12.20 (5V), R27.1, R30.1, R35.1, R36.1, RN1.1 (common), RN2.1 (common), RN3.1 (common), RN4.1 (common)
VSTB: C20.1, C21.1, J12.9 (5VSB), R38.2, R39.2, U8.9, U8.11, U8.13, U8.14 (VCC), U9.1 (~R), U9.10 (~S), U9.14 (VCC)
~0WS: J5.8 (~0WS/~SRDY), J6.8 (~0WS/~SRDY), J7.8 (~0WS/~SRDY), J8.8 (~0WS/~SRDY), J9.8 (~0WS/~SRDY), J10.8 (~0WS/~SRDY), RN1.4 (R3)
~DACK0: J5.70 (~DACK0), J6.70 (~DACK0), J7.70 (~DACK0), J8.70 (~DACK0), J9.70 (~DACK0), J10.70 (~DACK0)
~DACK1: J5.17 (~DACK1), J6.17 (~DACK1), J7.17 (~DACK1), J8.17 (~DACK1), J9.17 (~DACK1), J10.17 (~DACK1)
~DACK2: J5.26 (~DACK2), J6.26 (~DACK2), J7.26 (~DACK2), J8.26 (~DACK2), J9.26 (~DACK2), J10.26 (~DACK2)
~DACK3: J5.15 (~DACK3), J6.15 (~DACK3), J7.15 (~DACK3), J8.15 (~DACK3), J9.15 (~DACK3), J10.15 (~DACK3)
~DACK5: J5.72 (~DACK5), J6.72 (~DACK5), J7.72 (~DACK5), J8.72 (~DACK5), J9.72 (~DACK5), J10.72 (~DACK5)
~DACK6: J5.74 (~DACK6), J6.74 (~DACK6), J7.74 (~DACK6), J8.74 (~DACK6), J9.74 (~DACK6), J10.74 (~DACK6)
~DACK7: J5.76 (~DACK7), J6.76 (~DACK7), J7.76 (~DACK7), J8.76 (~DACK7), J9.76 (~DACK7), J10.76 (~DACK7)
~IOCS16: J5.64 (~IOCS16), J6.64 (~IOCS16), J7.64 (~IOCS16), J8.64 (~IOCS16), J9.64 (~IOCS16), J10.64 (~IOCS16), RN1.6 (R5)
~IOR: C51.1, J5.14 (~IOR), J6.14 (~IOR), J7.14 (~IOR), J8.14 (~IOR), J9.14 (~IOR), J10.14 (~IOR), RN3.5 (R4)
~IOW: J5.13 (~IOW), J6.13 (~IOW), J7.13 (~IOW), J8.13 (~IOW), J9.13 (~IOW), J10.13 (~IOW), RN3.4 (R3)
~IO_CH_CHK: J5.32 (~IOCHCK), J6.32 (~IOCHCK), J7.32 (~IOCHCK), J8.32 (~IOCHCK), J9.32 (~IOCHCK), J10.32 (~IOCHCK), RN1.2 (R1)
~KBC_GA20: RN2.5 (R4)
~KBC_RC: RN3.6 (R5)
~MEMCS16: J5.63 (~MEMCS16), J6.63 (~MEMCS16), J7.63 (~MEMCS16), J8.63 (~MEMCS16), J9.63 (~MEMCS16), J10.63 (~MEMCS16), RN1.5 (R4)
~MEMR: J5.89 (~MEMR), J6.89 (~MEMR), J7.89 (~MEMR), J8.89 (~MEMR), J9.89 (~MEMR), J10.89 (~MEMR), R35.2
~MEMW: J5.90 (~MEMW), J6.90 (~MEMW), J7.90 (~MEMW), J8.90 (~MEMW), J9.90 (~MEMW), J10.90 (~MEMW), R36.2
~PS_OFF: U9.2 (D), U9.6 (~Q), U9.13 (~R)
~PS_ON: J12.14 (~PS_ON), U9.5 (Q)
~REFRESH: J5.19 (~REFRESH), J6.19 (~REFRESH), J7.19 (~REFRESH), J8.19 (~REFRESH), J9.19 (~REFRESH), J10.19 (~REFRESH), RN1.8 (R7)
~RTC_IRQ8: RN2.6 (R5)
~SBHE: J5.81 (~SBHE), J6.81 (~SBHE), J7.81 (~SBHE), J8.81 (~SBHE), J9.81 (~SBHE), J10.81 (~SBHE)
~SMEMR: J5.12 (~SMEMR), J6.12 (~SMEMR), J7.12 (~SMEMR), J8.12 (~SMEMR), J9.12 (~SMEMR), J10.12 (~SMEMR), RN3.3 (R2)
~SMEMW: J5.11 (~SMEMW), J6.11 (~SMEMW), J7.11 (~SMEMW), J8.11 (~SMEMW), J9.11 (~SMEMW), J10.11 (~SMEMW), RN3.2 (R1)
